mikestrohofer-cloud/NMEA2000_CanSniffer_and_Custom_Marine_Dashboard_Display/Photos/Display Body 3.jpeg

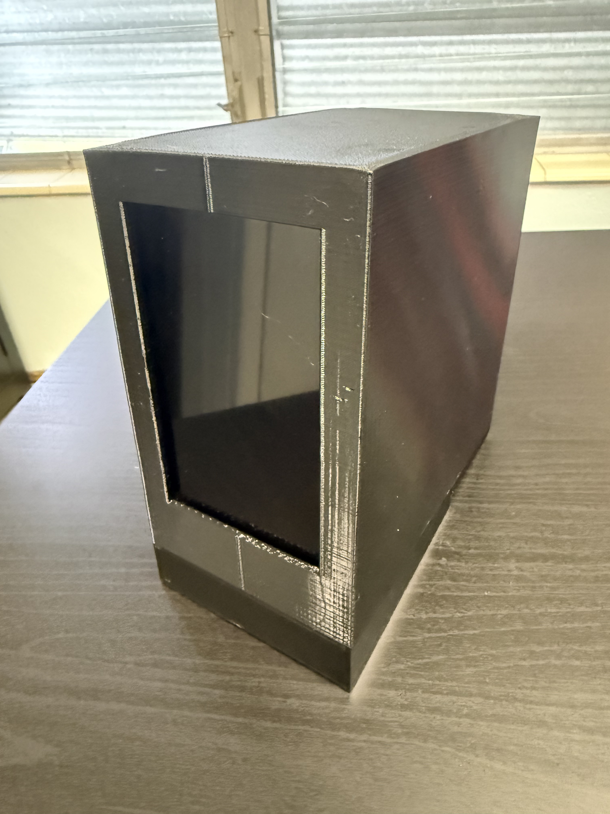
Photos/Display Body 3.jpeg
